akaStanley/NixieClock/Images/v1 big hr 602.png

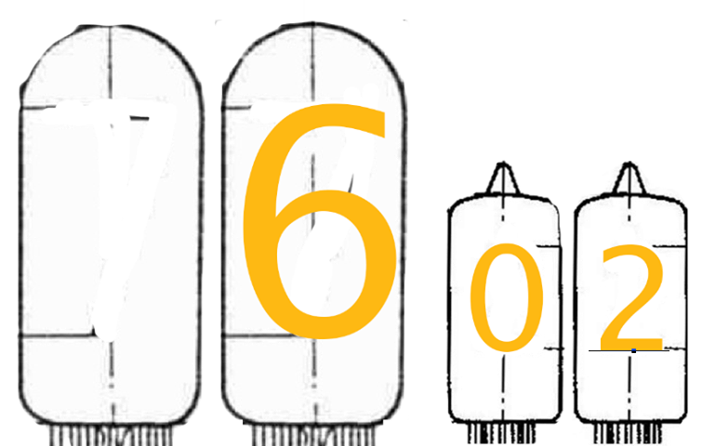
Images/v1 big hr 602.png
